insolace/ColorSynth-DMX/IMG/IMG_1336.jpg

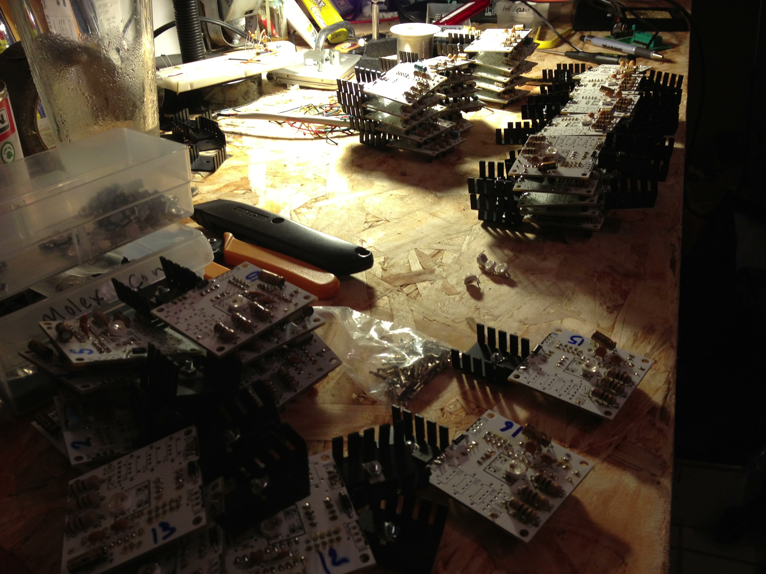
IMG/IMG_1336.jpg
