insolace/ColorSynth-DMX/IMG/IMG_1337.jpg

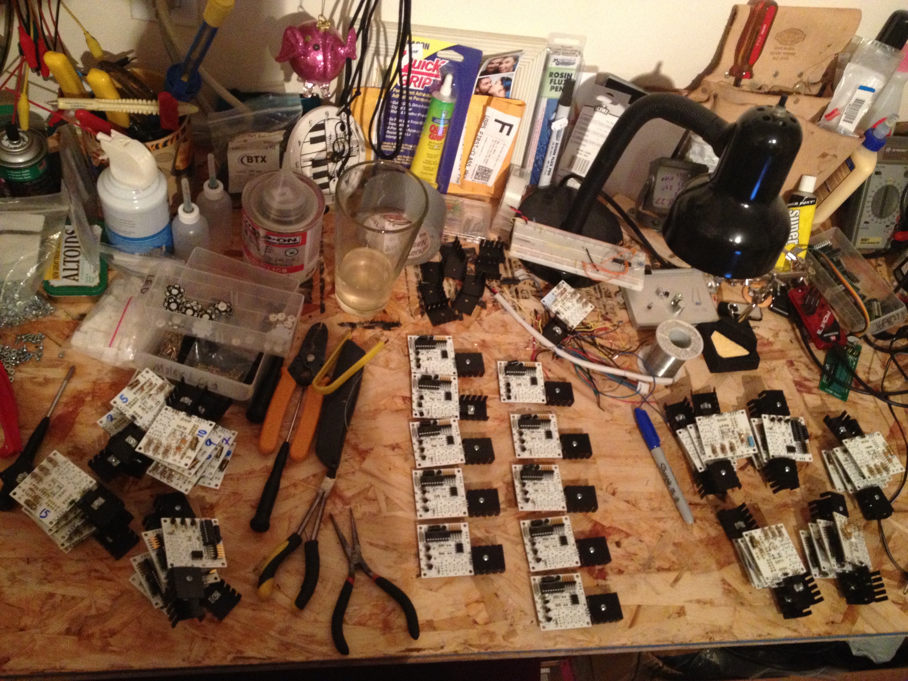
IMG/IMG_1337.jpg
