insolace/ColorSynth-DMX/PCB and Schematic/PCB export/DMX_RX_2RGB_BOT_PARTS.png

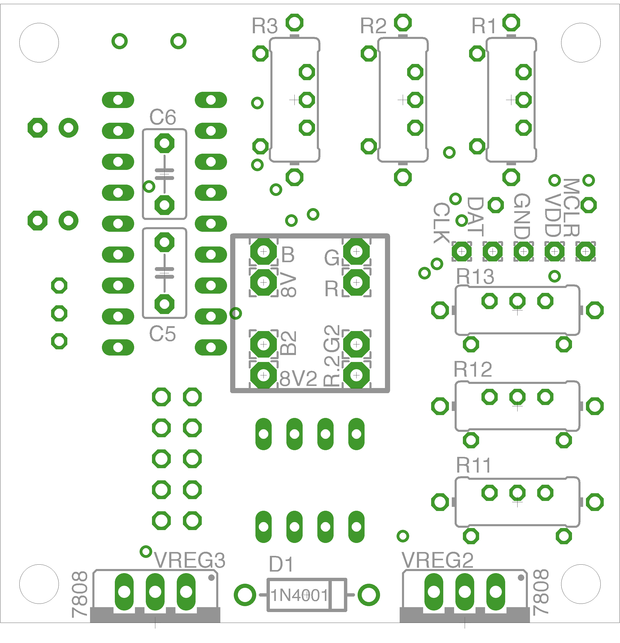
PCB and Schematic/PCB export/DMX_RX_2RGB_BOT_PARTS.png
